trezor/trezor-hardware/electronics/trezor_one/board.jpg

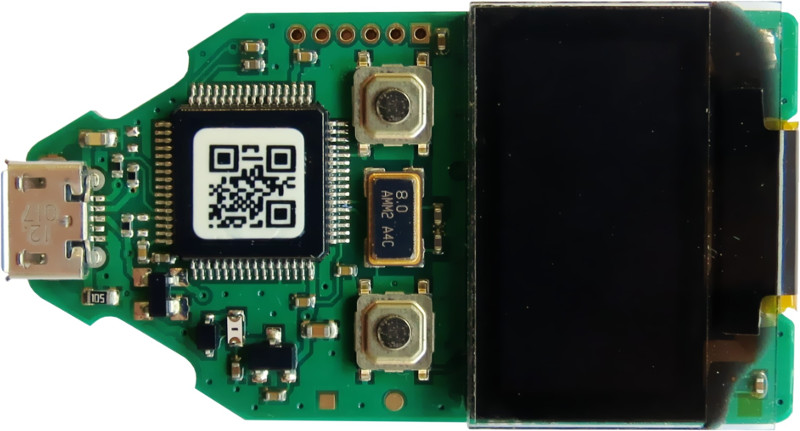
electronics/trezor_one/board.jpg
