trezor/trezor-hardware/electronics/trezor_one/programmer.sch.png

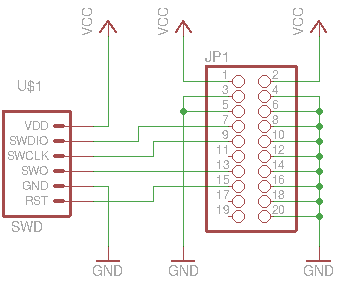
electronics/trezor_one/programmer.sch.png
