trezor/trezor-hardware/electronics/trezor_one/raspi.sch.png

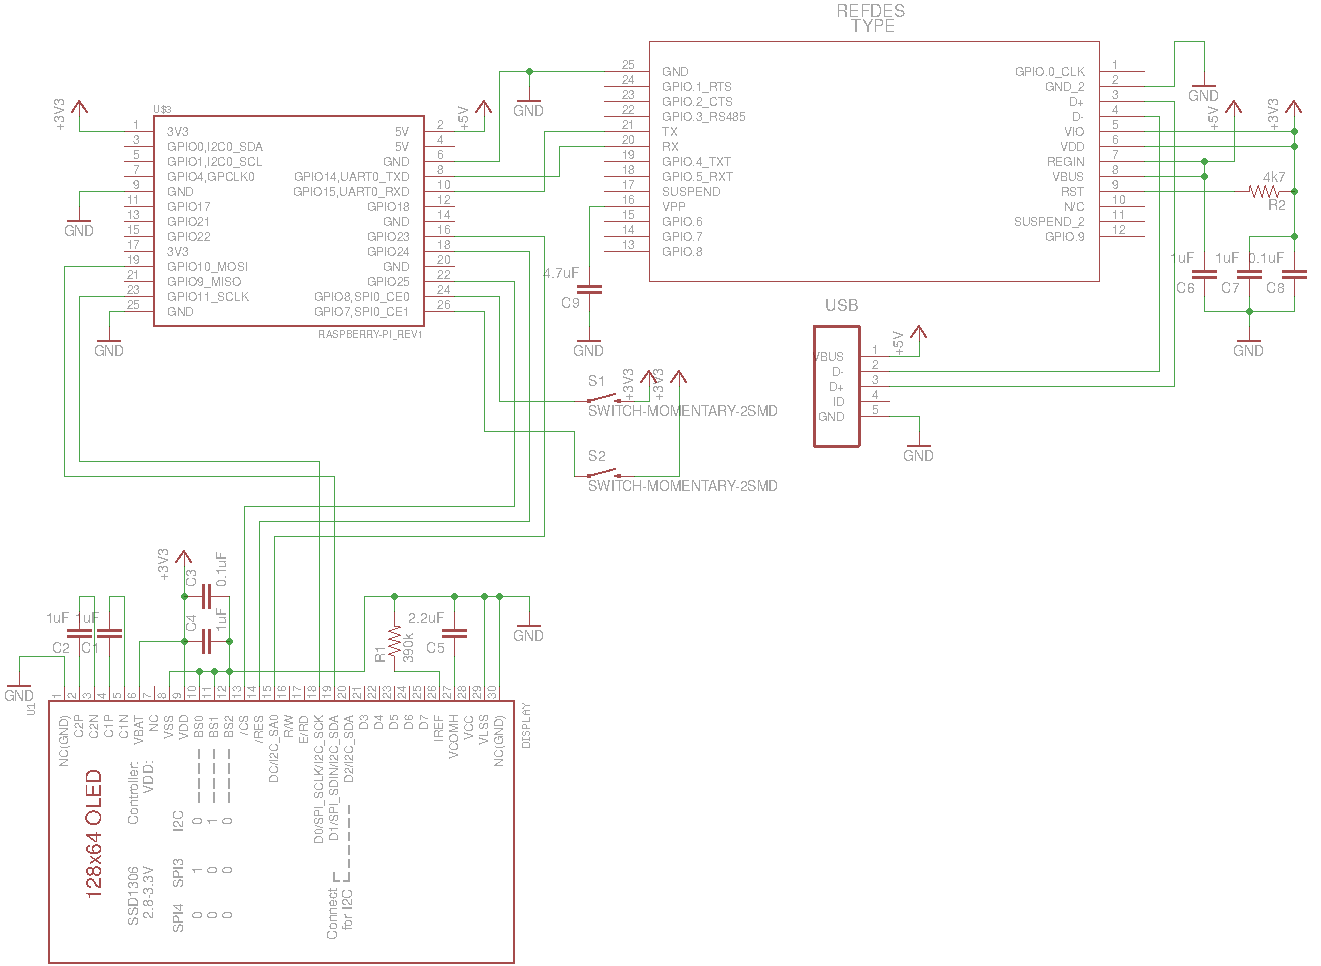
electronics/trezor_one/raspi.sch.png
