trezor/trezor-hardware/electronics/trezor_one/trezor_v1.1.brd.png

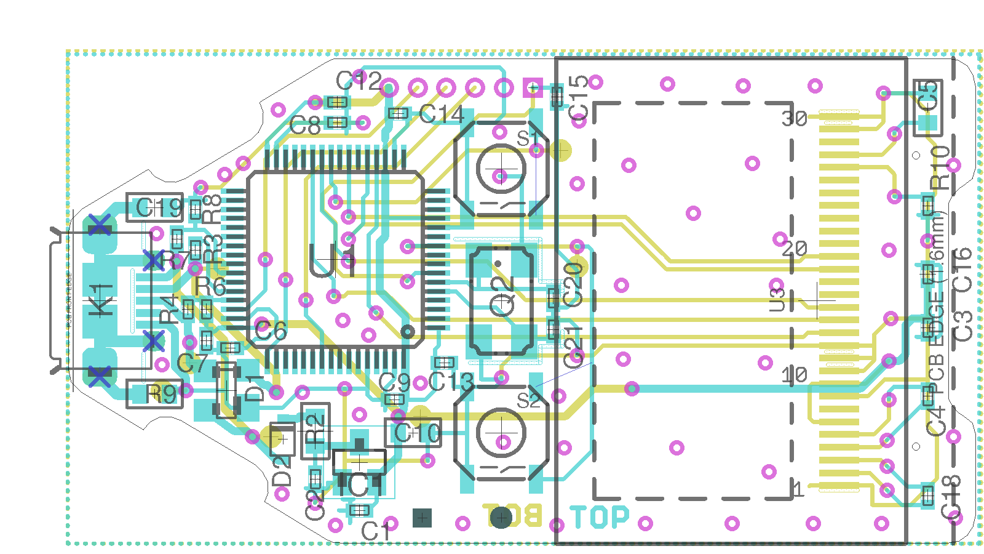
electronics/trezor_one/trezor_v1.1.brd.png
