trezor/trezor-hardware/electronics/trezor_one/trezor_v1.1.sch.png

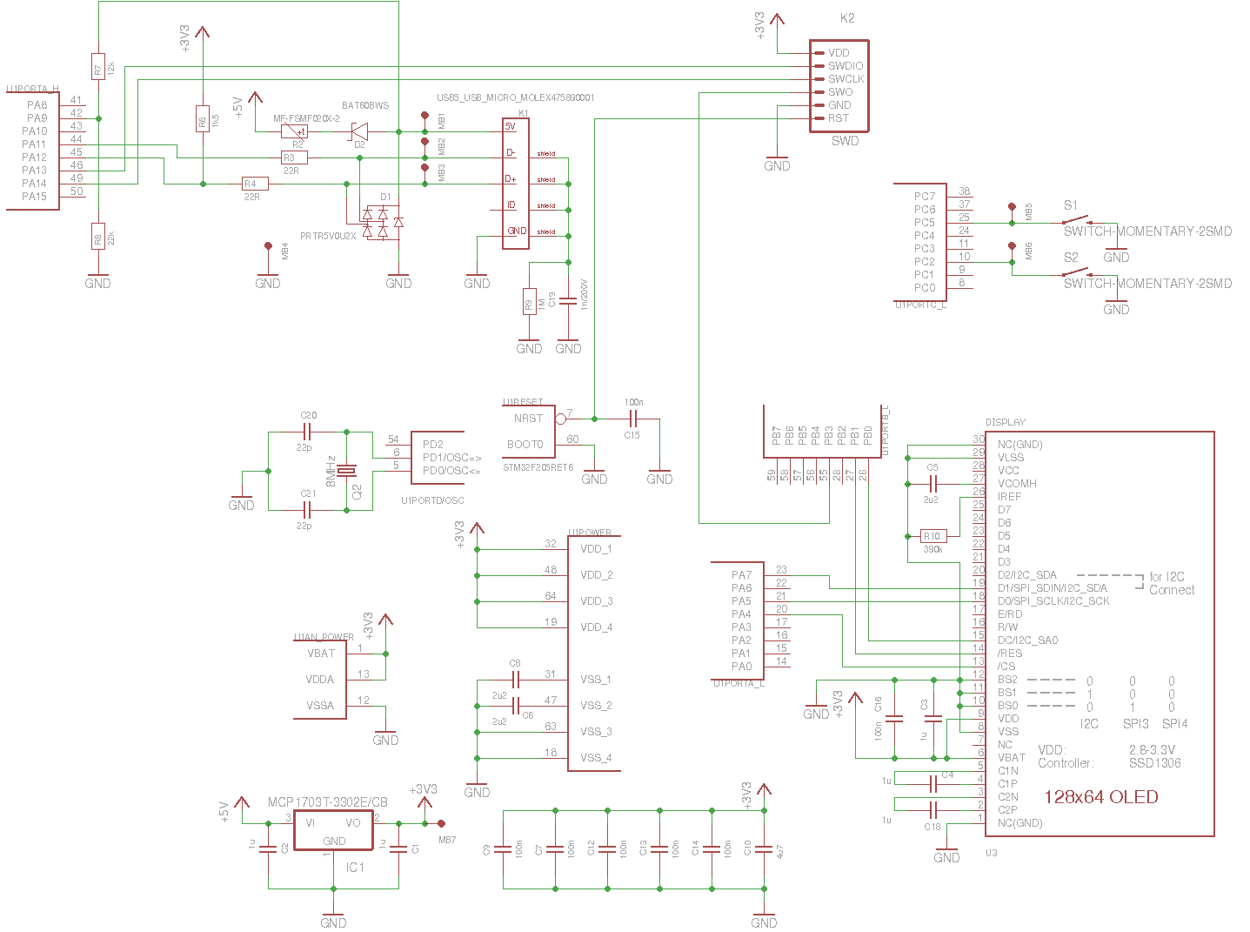
electronics/trezor_one/trezor_v1.1.sch.png
